danielsan80/minirace-gate/gate/src/startlights/sim/board.scad

use <../../../vendor/startlights/src/board/sim/board.scad>

module sim_startlights_board() {
    sim_board();
}
