danielsan80/minirace-gate/startlights/src/board/sim/board.scad

include <../../../config/parameters.scad>

use <../../../src/board/board.scad>

module sim_board_transform() {
    translate([board_offset.x, board_offset.y, -board_thick-board_startlights_gap])
    children();
}

module sim_board() {
    sim_board_transform()
    board();
}
