danielsan80/minirace-gate/controller-box/src/functions.scad

function hp(l) = pow(pow(l,2) + pow(l,2),1/2);
function hp2(l1, l2) = pow(pow(l1,2) + pow(l2,2),1/2);
