danielsan80/minirace-gate/controller-box/src/parts/print/box_bottom.scad

include <../../../config/parameters.scad>
use <../../parts/box_bottom.scad>

module print_box_bottom() {
    box_bottom();
};
