danielsan80/minirace-gate/controller-box/src/parts/print/box_top.scad

include <../../../config/parameters.scad>
use <../../parts/box_top.scad>

module print_box_top() {
    box_top();
};
