danielsan80/minirace-gate/controller-box/src/parts/print/box_top_led_hole_cap.scad

include <../../../config/parameters.scad>
use <../../parts/box_top_led_hole_cap.scad>

module print_box_top_led_hole_cap() {
    box_top_led_hole_cap();
};
