danielsan80/minirace-gate/controller-box/src/parts/sim/box_bottom.scad

include <../../../config/parameters.scad>
use <../../parts/box_bottom.scad>

module sim_box_bottom() {
    box_bottom();
}
