danielsan80/minirace-gate/controller-box/src/parts/sim/box_side_slide.scad

include <../../../config/parameters.scad>
use <../../parts/box_side_slide.scad>

module sim_box_side_slide() {
    box_side_slide();
};
