danielsan80/minirace-gate/controller-box/build/scad/print/box/box_bottom.scad

use <../../../../src/parts/print/box_bottom.scad>

print_box_bottom();
