danielsan80/minirace-gate/controller-box/build/scad/print/box/box_side_slide.scad

use <../../../../src/parts/print/box_side_slide.scad>

print_box_side_slide();
