danielsan80/minirace-gate/controller-box/build/scad/print/box/box_top.scad

use <../../../../src/parts/print/box_top.scad>

print_box_top();
