danielsan80/minirace-gate/controller-box/build/scad/print/box/box_top_led_hole_cap.scad

use <../../../../src/parts/print/box_top_led_hole_cap.scad>

print_box_top_led_hole_cap();
