danielsan80/minirace-gate/car/main.scad

use <src/cars.scad>

cars(5);
