danielsan80/minirace-gate/gate/src/startlights/hanger.scad

include <../../config/parameters.scad>
use <../../vendor/startlights/src/hanger/clip.scad>
use <../../vendor/startlights/src/hanger/rod.scad>
use <../../vendor/startlights/src/hanger/clip_rod_joint.scad>

module startlights_hanger_clip_c(w=bar_wrapper_w) {
    hanger_clip_c(w=w);
}

module startlights_hanger_clip() {
    hanger_clip();
}

module startlights_hanger_rod() {
    hanger_rod();
}

function startlights_hanger_clip_rod_joint_pixel() = hanger_clip_rod_joint_pixel();
