danielsan80/minirace-gate/gate/src/startlights/values.scad

include <../../vendor/startlights/config/parameters.scad>

function startlights_board_hole_offset() = board_hole_offset;
function startlights_board_l() = board_l;
function startlights_board_margin() = board_margin;
function startlights_board_hole_d() = board_hole_d;
function startlights_board_startlights_gap() = board_startlights_gap;
function startlights_board_thick() = board_thick;
function startlights_startlights_height() = startlights_height;
function startlights_startlights_length() = startlights_length;
