danielsan80/minirace-gate/src/interparts/print/bar_c_hook.scad

use <../../interparts/traverse-startlights.scad>

module print_bar_c_hook() {
    bar_c_hook();
}
