danielsan80/minirace-gate/startlights/src/hanger/clip_rod_joint.scad

include <../../config/parameters.scad>
use <../../src/joint/ct_slide.scad>

function hanger_clip_rod_joint_pixel() = ct_slide_pixel();
