danielsan80/minirace-gate/gate/src/basement/print/_basement.scad

include <../../../config/parameters.scad>
use <../../basement/_basement.scad>

module _print_basement() {
    _basement();
}
