danielsan80/minirace-gate/gate/src/basement/print/basement_ground_guide.scad

include <../../../config/parameters.scad>
use <../../basement/basement_ground_guide.scad>

module print_basement_bolting_guide() {
    basement_bolting_guide();
}
