danielsan80/minirace-gate/gate/src/basement/sim/_basement.scad

include <../../../config/parameters.scad>
use <../../basement/_basement.scad>
use <../../basement/sim/_basement_transform.scad>

module _sim_basement_L() {
    _basement();
}

module _sim_basement_R(startline_l=startline_l) {
    _sim_basement_R_transform(startline_mode="basement", startline_l=startline_l)
    _basement();
}
